Batterhead221/port_sprite/Outputs/IMG/L1_SIG.png

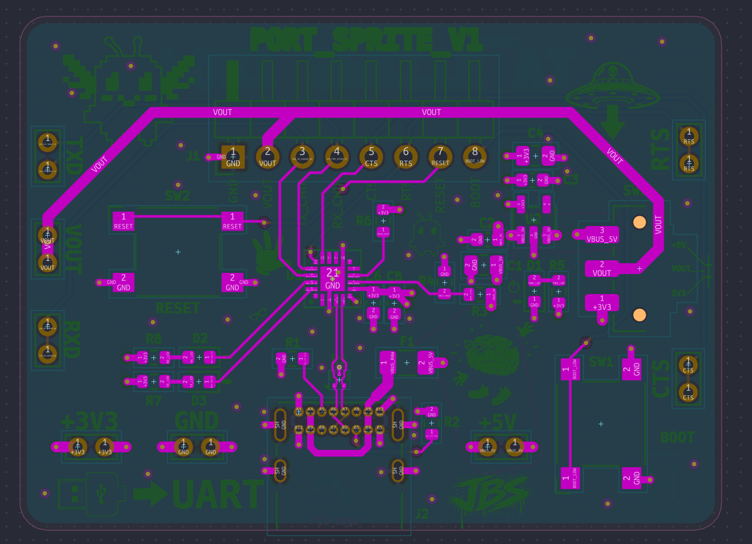
Outputs/IMG/L1_SIG.png
