Batterhead221/port_sprite/Outputs/IMG/L2_GND.png

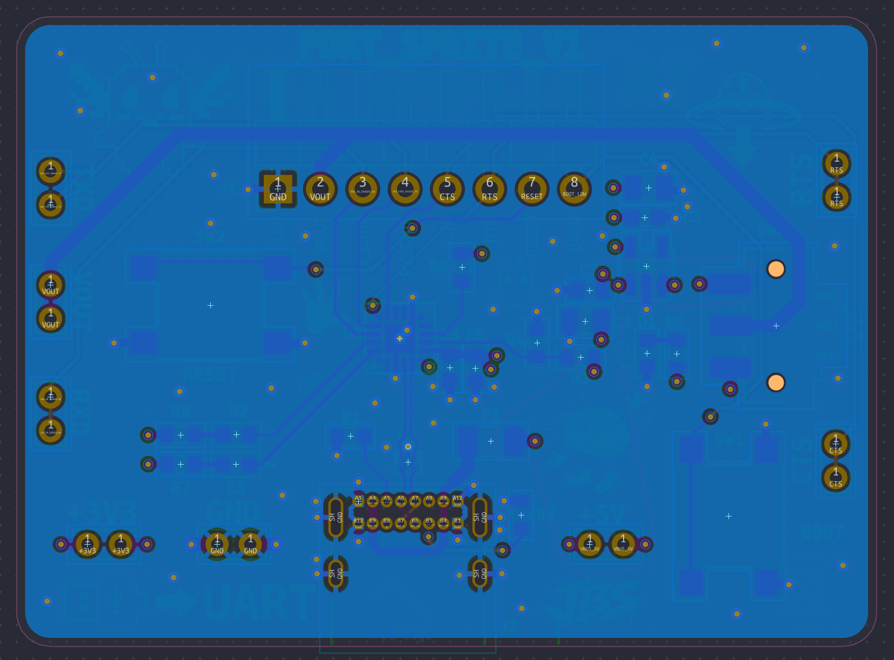
Outputs/IMG/L2_GND.png
