Batterhead221/port_sprite/Outputs/IMG/L3_PWR.png

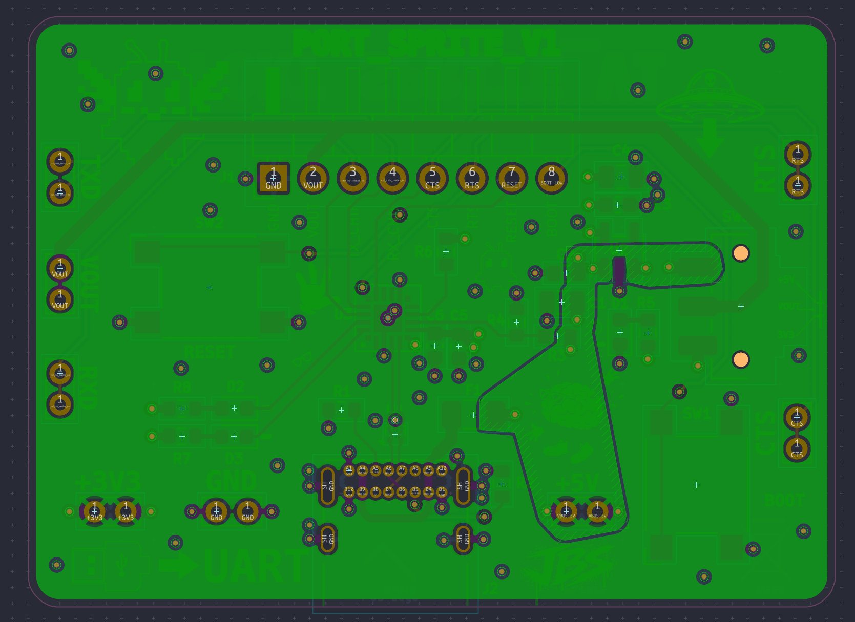
Outputs/IMG/L3_PWR.png
