Batterhead221/port_sprite/Outputs/IMG/L4_MIX.png

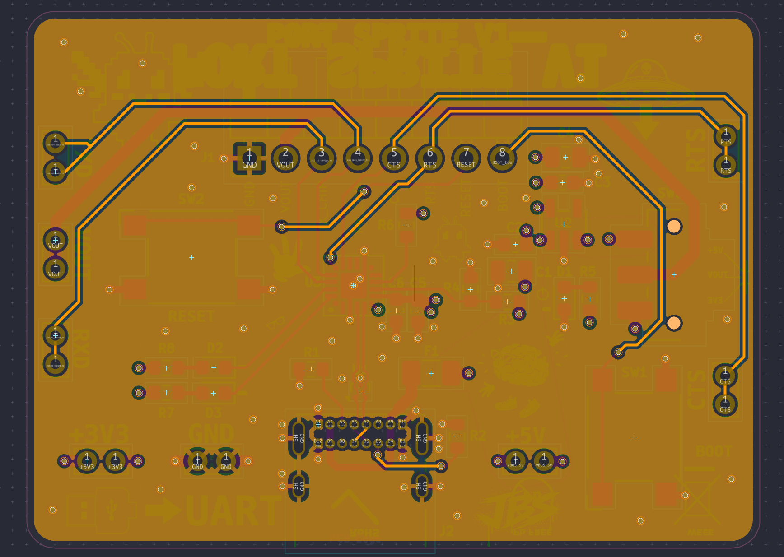
Outputs/IMG/L4_MIX.png
