Batterhead221/port_sprite/Outputs/IMG/SCHEMATIC.png

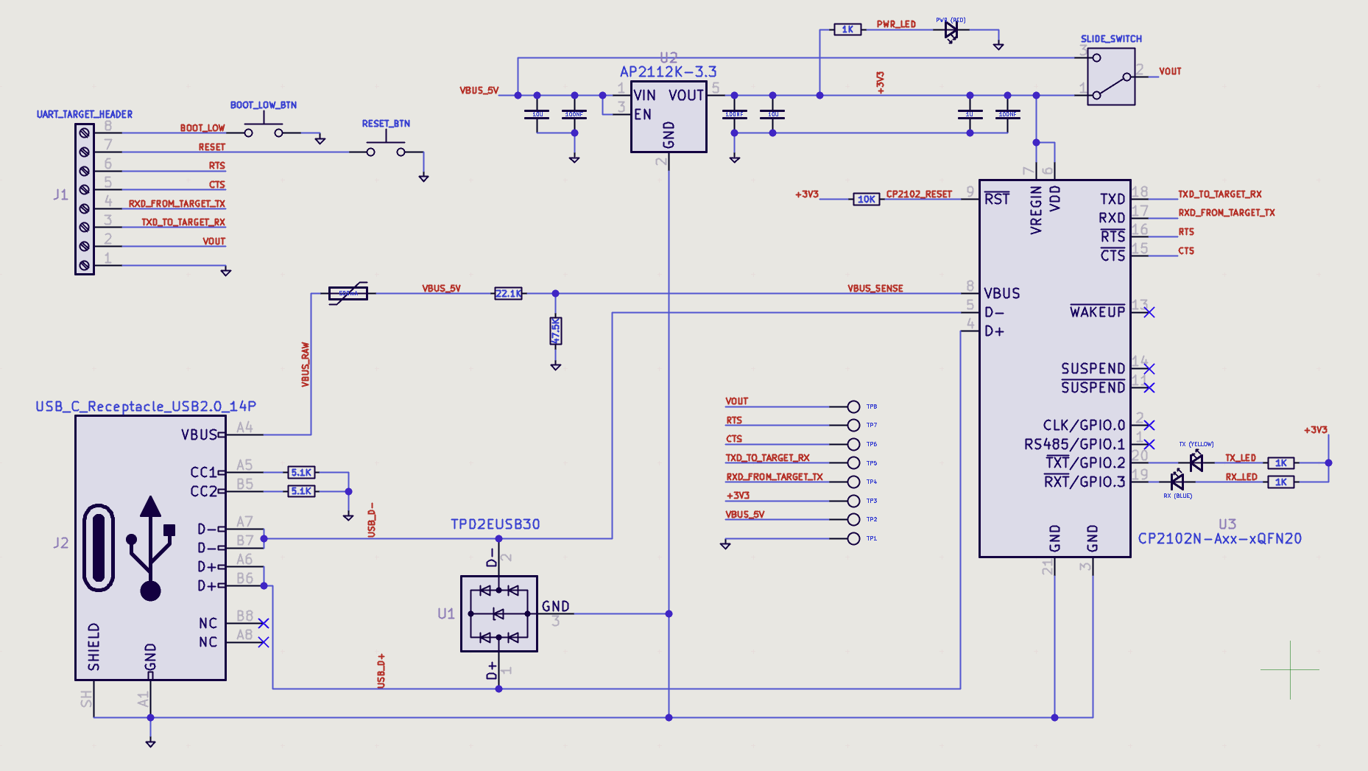
Outputs/IMG/SCHEMATIC.png
